0x3333/powermeter/src/config.h

#ifndef _CONFIG_H_
#define _CONFIG_H_

// ------------------------------------------------------------------------
#define CONFIG_MINIMAL_SYSTEM 1
#define CONFIG_PIN 1
#define CONFIG_UART 1
#define CONFIG_I2C 1
#define CONFIG_START_CONSOLE CONFIG_START_CONSOLE_NONE
#define CONFIG_MODULE_INIT_RWLOCK 1

// ------------------------------------------------------------------------

#endif /* _CONFIG_H_ */
