0x3333/powermeter/src/i2c.h

#ifndef _I2C_H_
#define _I2C_H_

// ------------------------------------------------------------------------
#define SLAVE_ADDRESS 0x33

// ------------------------------------------------------------------------
void pz_i2c_setup();

void pz_i2c_start();

// ------------------------------------------------------------------------

#endif /* _I2C_H_ */
